Squalius-cephalus/silli18/firmware/silli18/keymaps/vial/config.h

/* SPDX-License-Identifier: GPL-2.0-or-later */

#pragma once

#define VIAL_KEYBOARD_UID {0xD4, 0x96, 0x0B, 0xC3, 0xDD, 0x29, 0xEE, 0x81}

#define VIAL_UNLOCK_COMBO_ROWS { 0, 1 }
#define VIAL_UNLOCK_COMBO_COLS { 1, 1 }
